thebenheckshow/204-tbhs-zx-kit/Charger_Regulator/5VRegulator/s7v7f5-schematic.pdf

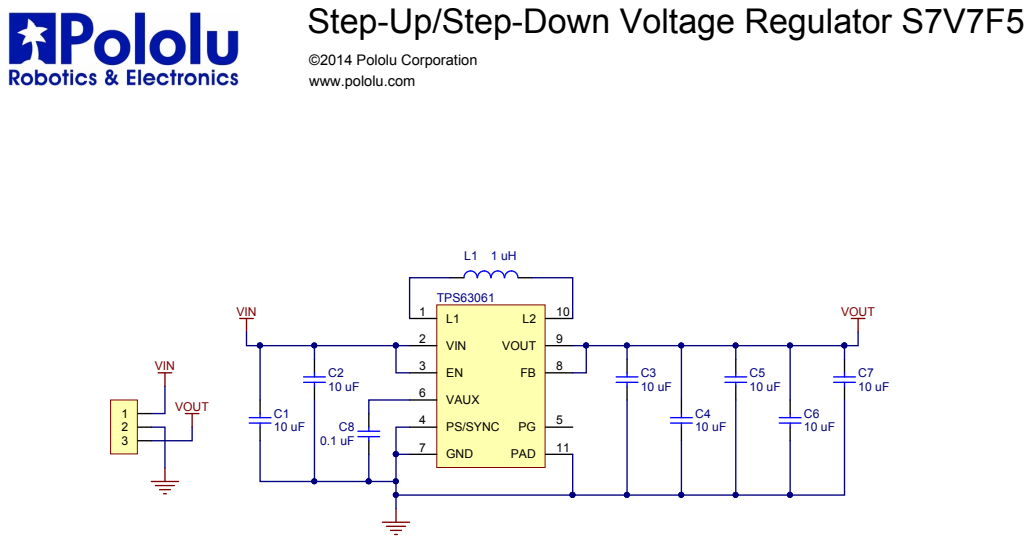
[picture p11: page 1]

Step-Up/Step-Down Voltage Regulator S7V7F5 ©2014 Pololu Corporation
