thebenheckshow/204-tbhs-zx-kit/parts/Speaker 25R0930.pdf

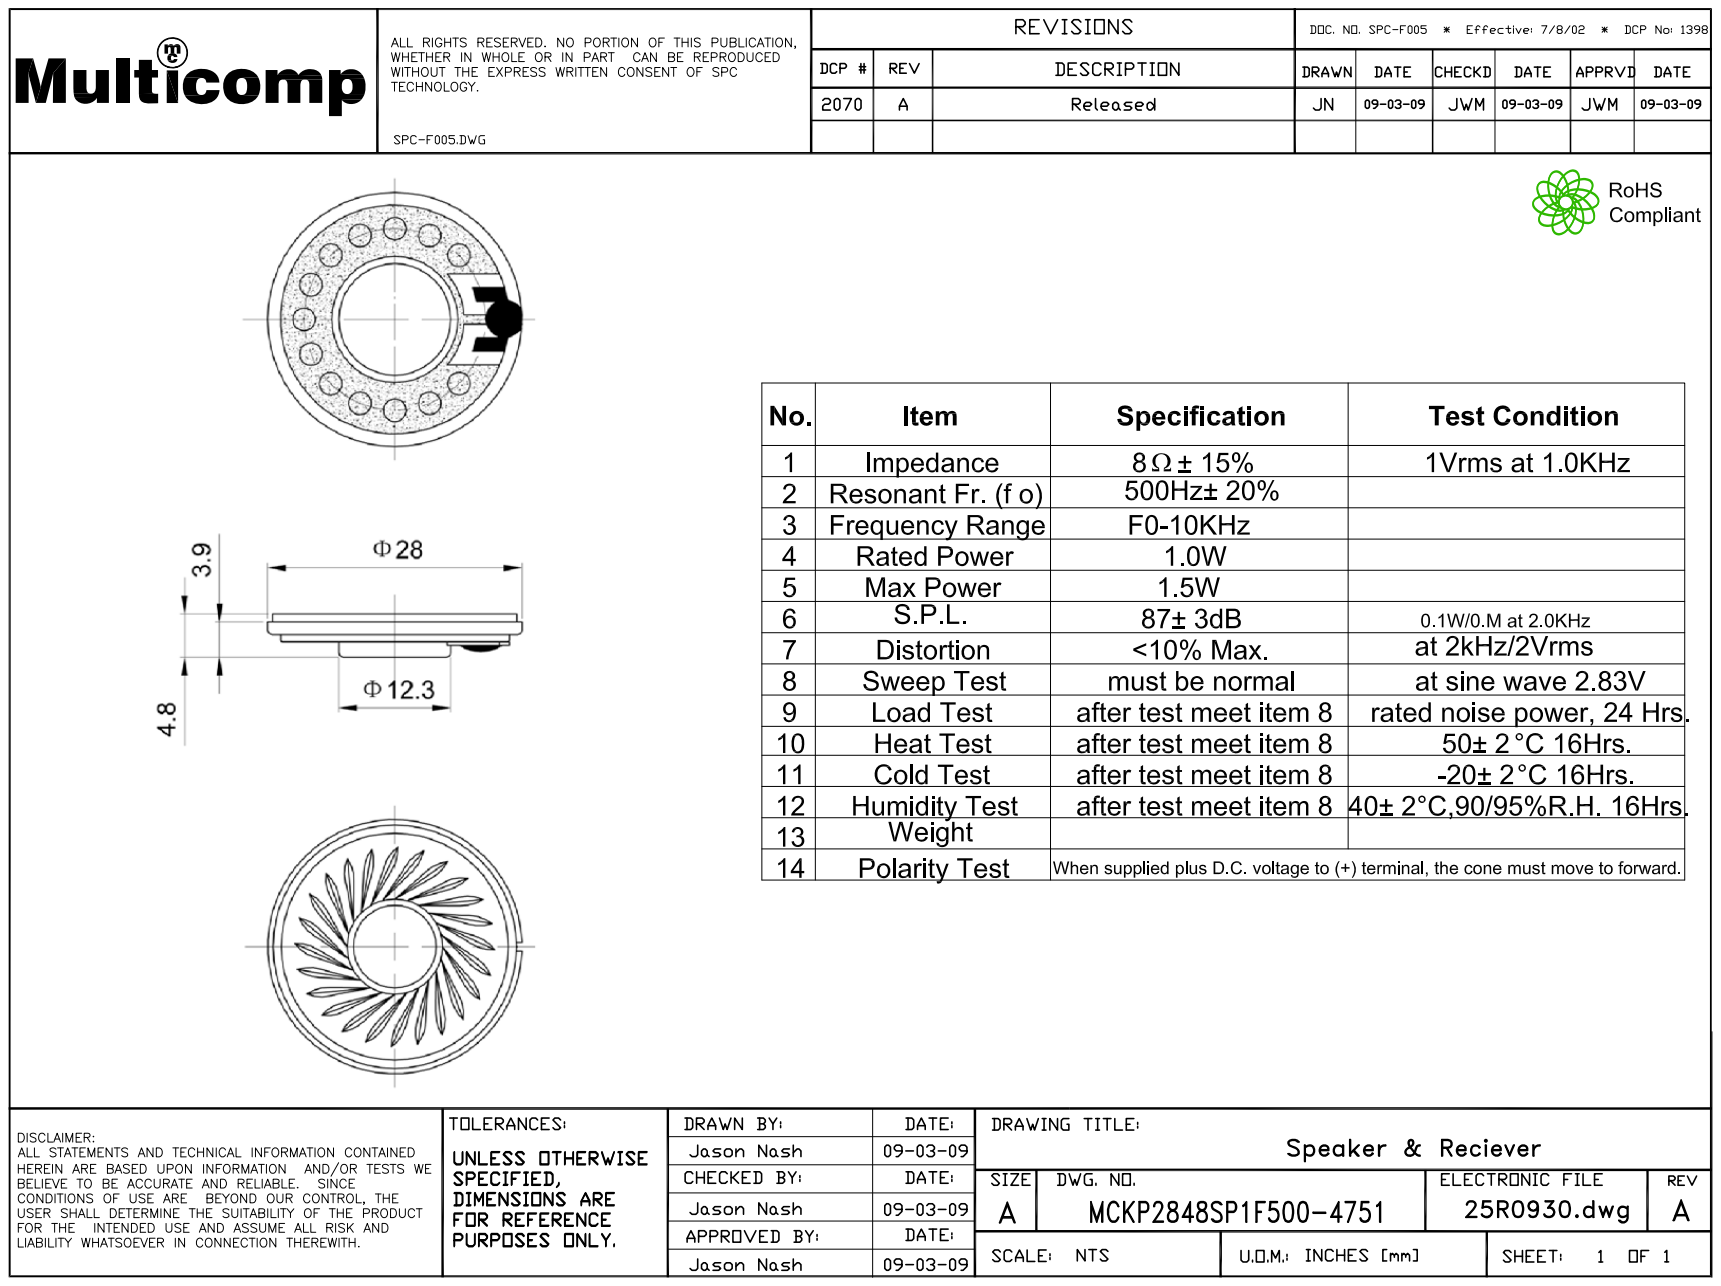
[picture p12: page 1]
